Helmetboy/PrintedLock/lock-acetone.jpg

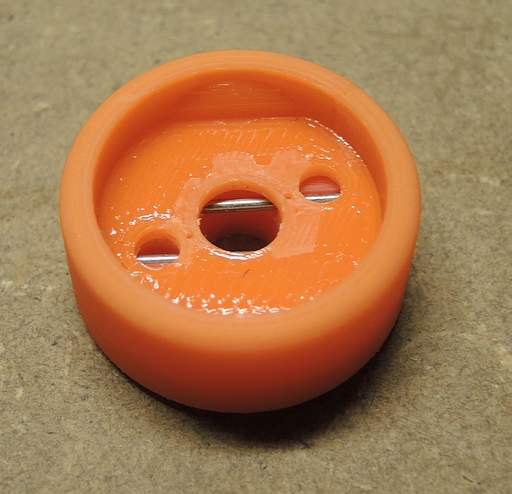
lock-acetone.jpg
