Helmetboy/PrintedLock/lock-colors_and_shapes.jpg

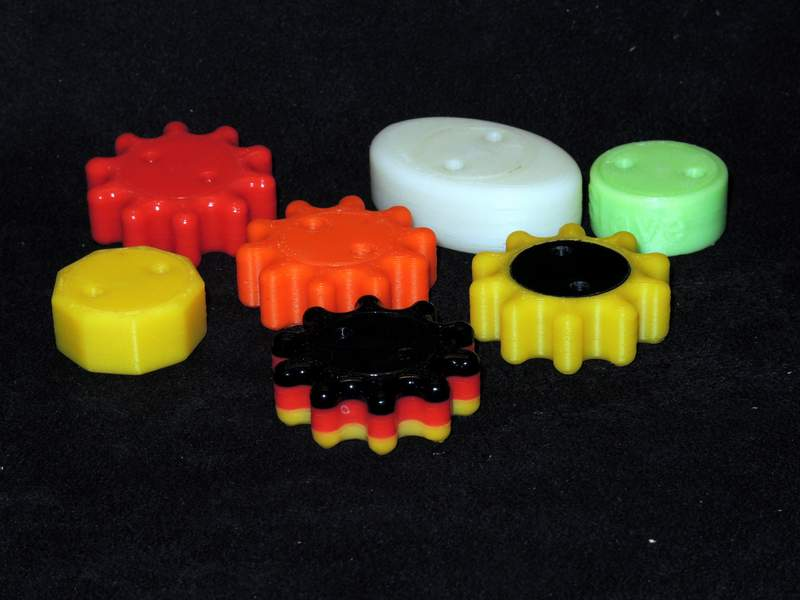
lock-colors_and_shapes.jpg
