Helmetboy/PrintedLock/pins-chamfered.jpg

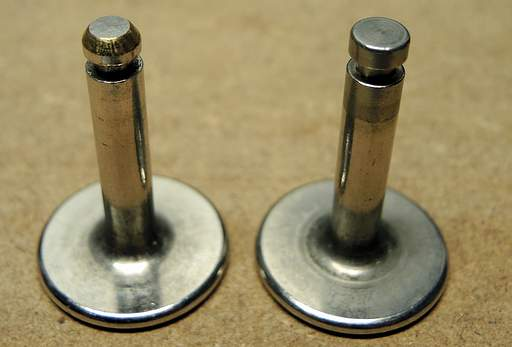
pins-chamfered.jpg
