Helmetboy/PrintedLock/wire-cut.jpg

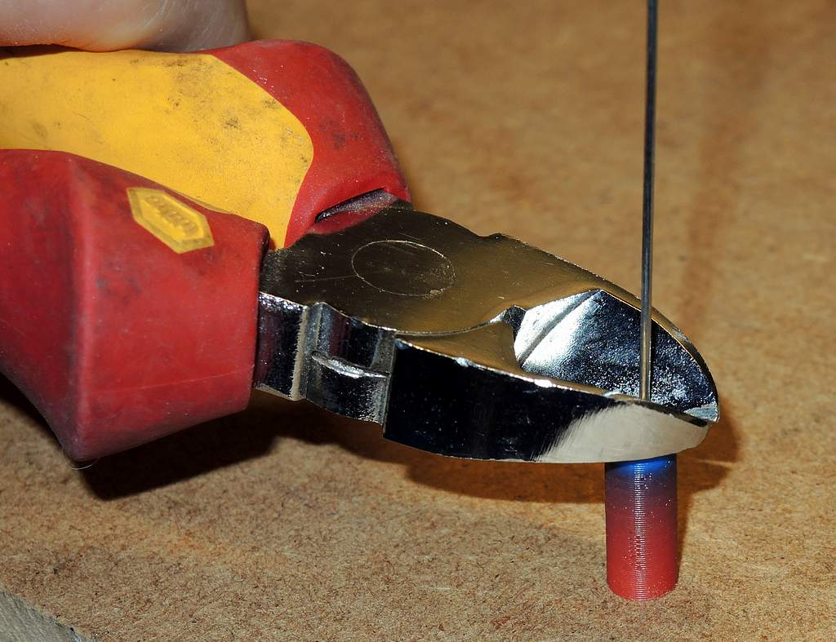
wire-cut.jpg
