Helmetboy/PrintedLock/lock-springs-installed.jpg

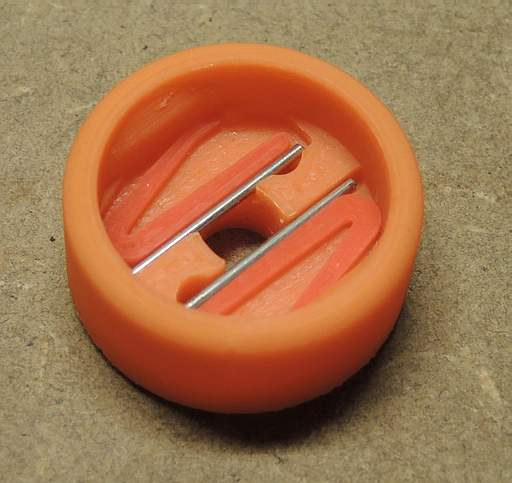
lock-springs-installed.jpg
