Helmetboy/PrintedLock/lock-testfit.jpg

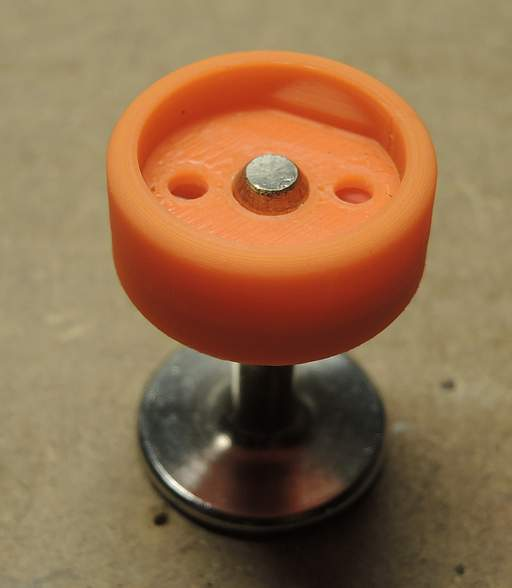
lock-testfit.jpg
